pcarlss/Solar-Panel-Cleaning-Drone/Videos and Pictures/image.png

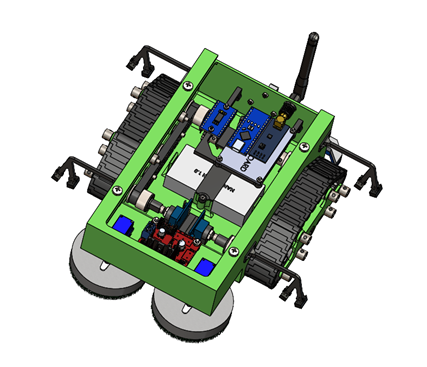
Videos and Pictures/image.png
