pcarlss/Solar-Panel-Cleaning-Drone/Simulations/Rover-Simulation/rover_mission.gif

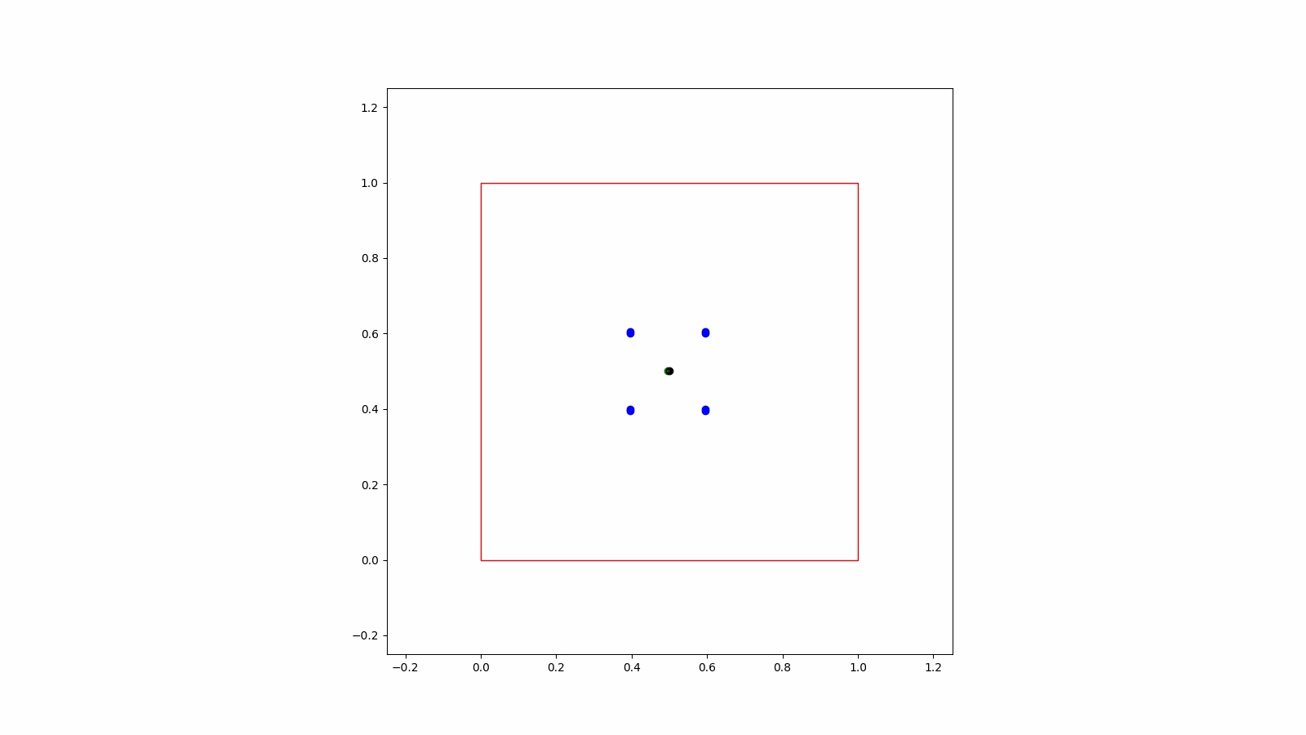
Simulations/Rover-Simulation/rover_mission.gif
