pcarlss/Solar-Panel-Cleaning-Drone/Videos and Pictures/ISO_FINAL.JPG

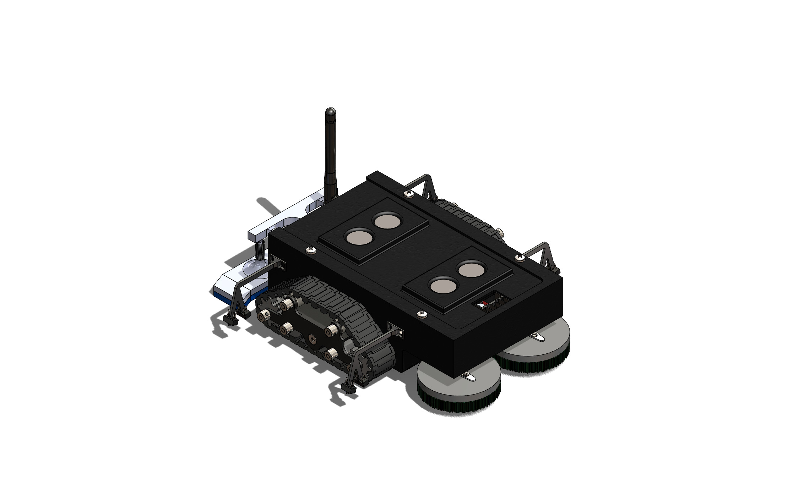
Videos and Pictures/ISO_FINAL.JPG
