pcarlss/Solar-Panel-Cleaning-Drone/KiCad/Complete-Drone-Systems/DronePower.kicad_sch

## KiCad design KiCad/Complete-Drone-Systems/DronePower.kicad_sch (2025-04-15, an earlier design)

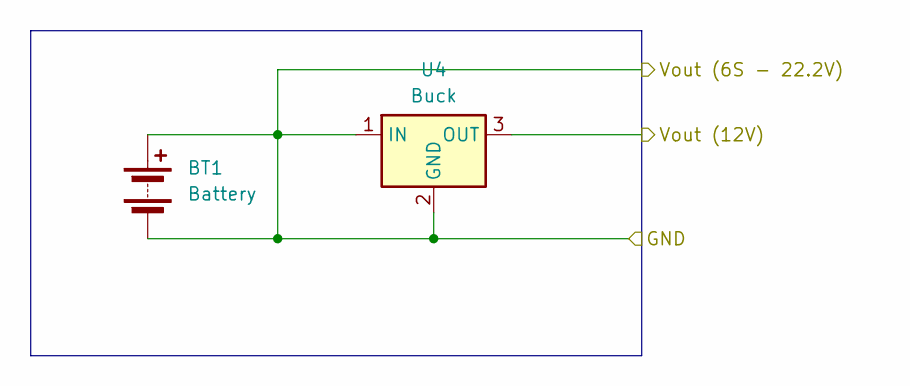
[picture p38: schematic DronePower.kicad_sch]

Parts:
BT1: Battery
U4: Buck; Converter_DCDC_Murata_OKI-78SR_Vertical

Connections:
GND: BT1.1 (+), BT1.2 (-), U4.1 (IN), U4.2 (GND)
Vout (12V): U4.3 (OUT)
