pcarlss/Solar-Panel-Cleaning-Drone/KiCad/Complete-Drone-Systems/Flight.kicad_sch

## KiCad design KiCad/Complete-Drone-Systems/Flight.kicad_sch (2025-01-29)

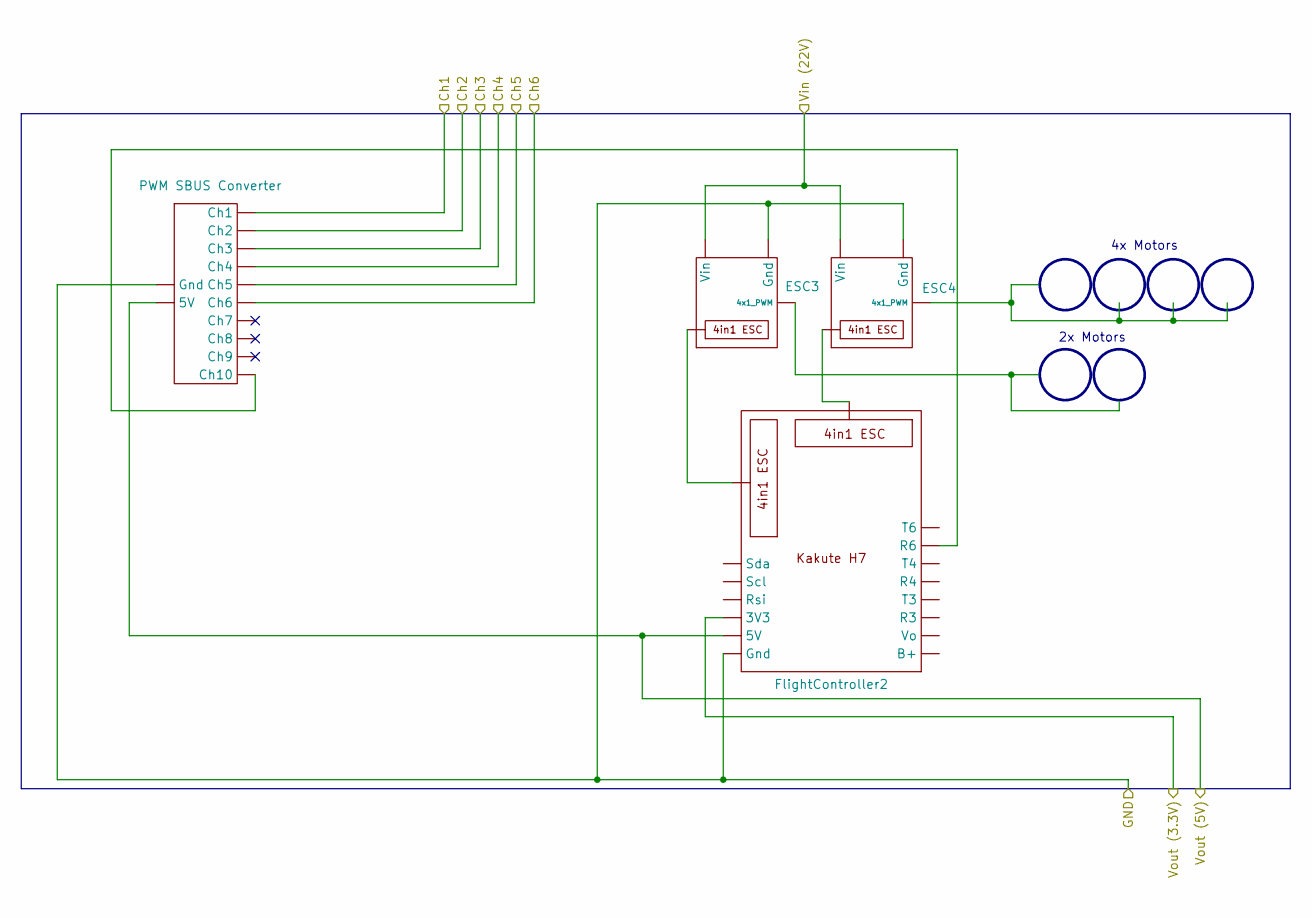
[picture p39: schematic Flight.kicad_sch]

Parts:
ESC3, ESC4: (no value)
FlightController2: (no value)
U6: PWM SBUS Converter

Connections:
Ch1: U6.
Ch2: U6.
Ch3: U6.
Ch4: U6.
Ch5: U6.
Ch6: U6.
GND: ESC3., ESC4., FlightController2., U6.
unnamed: ESC3., FlightController2.
unnamed: ESC4., FlightController2.
unnamed: FlightController2., U6.
Vin (22V): ESC3., ESC4.
Vout (3.3V): FlightController2.
Vout (5V): FlightController2., U6.

Notes on the sheet:
2x Motors
4x Motors
