pcarlss/Solar-Panel-Cleaning-Drone/KiCad/Complete-Drone-Systems/REleaseMechanism.kicad_sch

## KiCad design KiCad/Complete-Drone-Systems/REleaseMechanism.kicad_sch (2025-01-29)

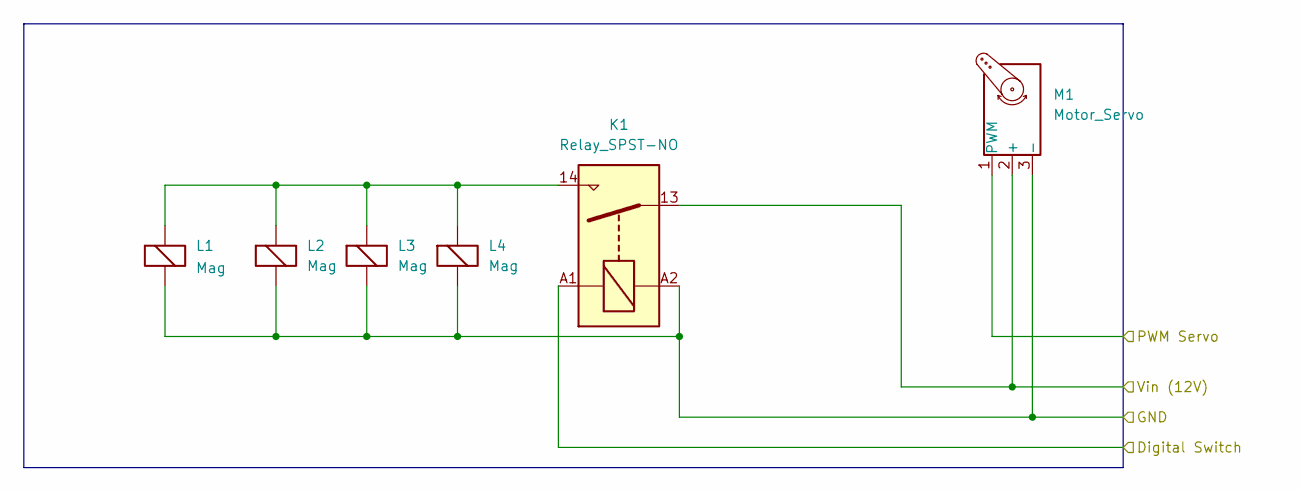
[picture p40: schematic REleaseMechanism.kicad_sch]

Parts:
K1: Relay_SPST-NO
L1, L2, L3, L4: Mag
M1: Motor_Servo

Connections:
Digital Switch: K1.A1
GND: K1.A2, L1.2 (+), L2.2 (+), L3.2 (+), L4.2 (+), M1.3 (-)
unnamed: K1.14, L1.1 (-), L2.1 (-), L3.1 (-), L4.1 (-)
PWM Servo: M1.1 (PWM)
Vin (12V): K1.13, M1.2 (+)
