pcarlss/Solar-Panel-Cleaning-Drone/KiCad/Complete-Drone-Systems/RadioModule.kicad_sch

## KiCad design KiCad/Complete-Drone-Systems/RadioModule.kicad_sch (2025-01-29)

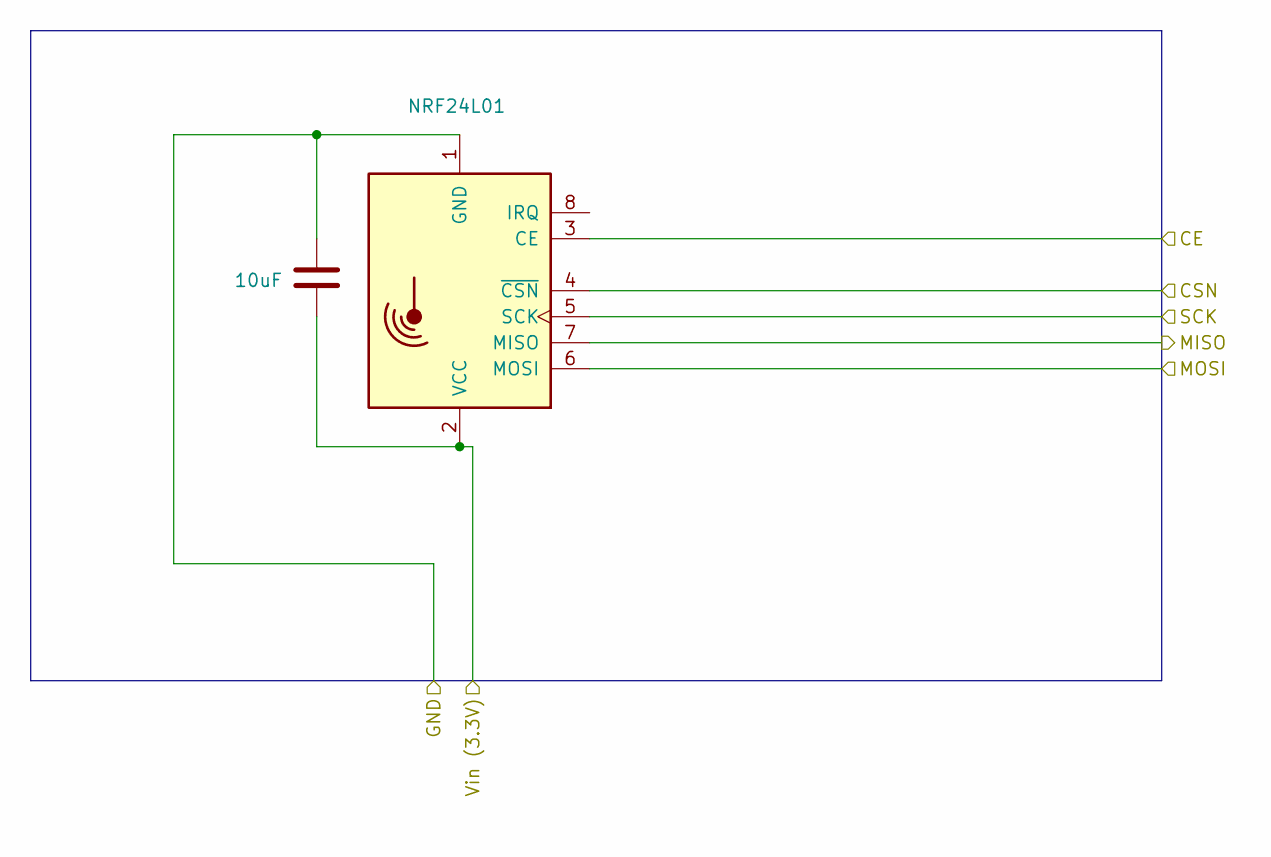
[picture p41: schematic RadioModule.kicad_sch]

Parts:
C2: 10uF
U3: NRF24L01; nRF24L01_Breakout

Connections:
CE: U3.3 (CE)
CSN: U3.4 (~CSN)
GND: C2.2, U3.1 (GND)
MISO: U3.7 (MISO)
MOSI: U3.6 (MOSI)
SCK: U3.5 (SCK)
Vin (3.3V): C2.1, U3.2 (VCC)
