pcarlss/Solar-Panel-Cleaning-Drone/KiCad/Complete-Rover-Systems/CleaningSystem.kicad_sch

## KiCad design KiCad/Complete-Rover-Systems/CleaningSystem.kicad_sch (2025-01-29)

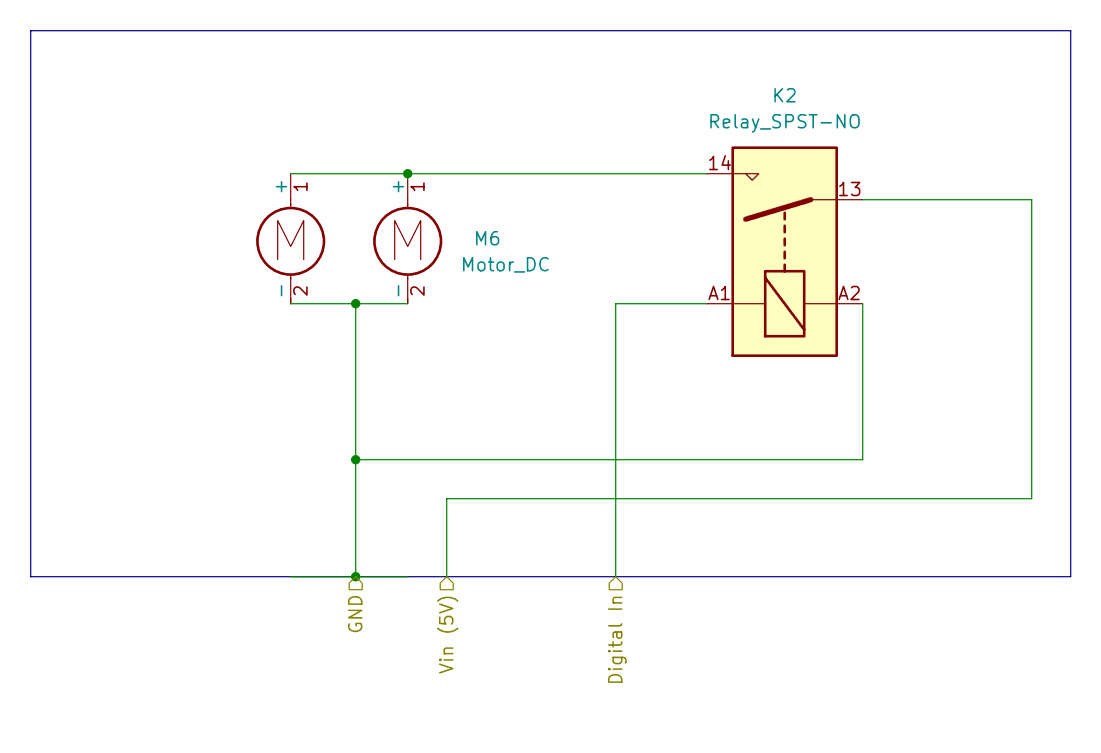
[picture p42: schematic CleaningSystem.kicad_sch]

Parts:
K2: Relay_SPST-NO
M5, M6: Motor_DC

Connections:
Digital In: K2.A1
GND: K2.A2, M5.2 (-), M6.2 (-)
unnamed: K2.14, M5.1 (+), M6.1 (+)
Vin (5V): K2.13
