pcarlss/Solar-Panel-Cleaning-Drone/KiCad/Complete-Rover-Systems/EdgeDetection.kicad_sch

## KiCad design KiCad/Complete-Rover-Systems/EdgeDetection.kicad_sch (2025-04-15, an earlier design)

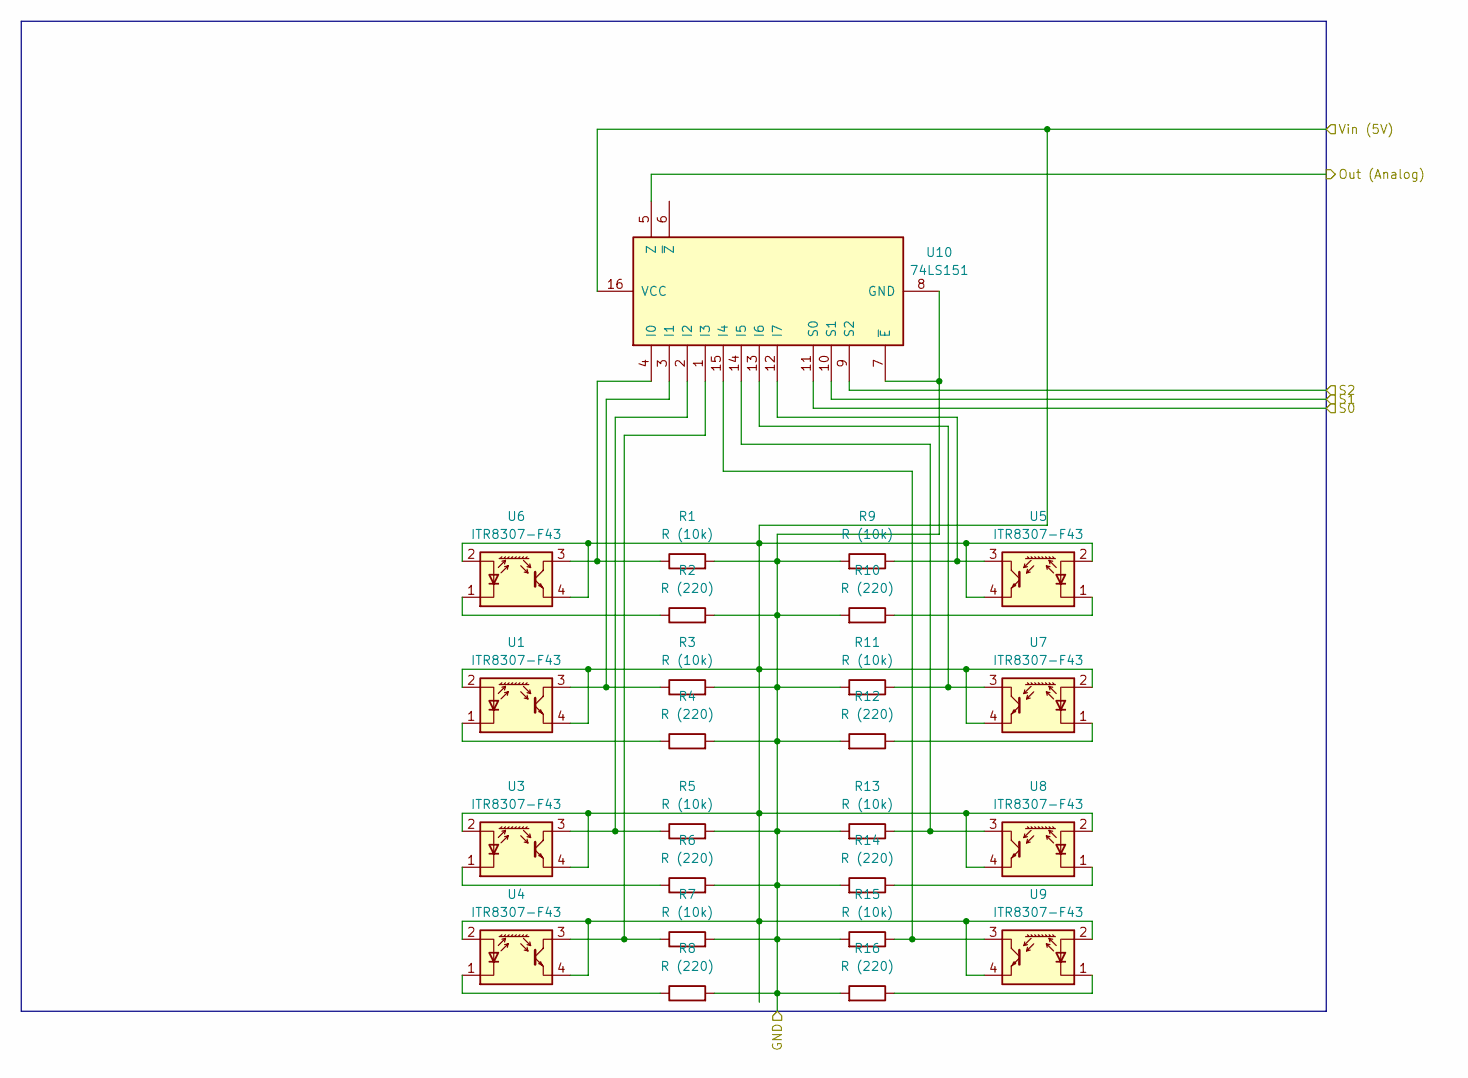
[picture p43: schematic EdgeDetection.kicad_sch]

Parts:
R1, R3, R5, R7, R9, R11, R13, R15: R (10k)
R2, R4, R6, R8, R10, R12, R14, R16: R (220)
U1, U3, U4, U5, U6, U7, U8, U9: ITR8307-F43; Everlight_ITR8307F43
U10: 74LS151

Connections:
GND: R1.2, R2.2, R3.2, R4.2, R5.2, R6.2, R7.2, R8.2, R9.2, R10.2, R11.2, R12.2, R13.2, R14.2, R15.2, R16.2, U10.7 (~E), U10.8 (GND)
unnamed: R1.1, U6.3 (C), U10.4 (I0)
unnamed: R2.1, U6.1 (K)
unnamed: R3.1, U1.3 (C), U10.3 (I1)
unnamed: R4.1, U1.1 (K)
unnamed: R5.1, U3.3 (C), U10.2 (I2)
unnamed: R6.1, U3.1 (K)
unnamed: R7.1, U4.3 (C), U10.1 (I3)
unnamed: R8.1, U4.1 (K)
unnamed: R9.1, U5.3 (C), U10.12 (I7)
unnamed: R10.1, U5.1 (K)
unnamed: R11.1, U7.3 (C), U10.13 (I6)
unnamed: R12.1, U7.1 (K)
unnamed: R13.1, U8.3 (C), U10.14 (I5)
unnamed: R14.1, U8.1 (K)
unnamed: R15.1, U9.3 (C), U10.15 (I4)
unnamed: R16.1, U9.1 (K)
Out (Analog): U10.5 (Z)
S0: U10.11 (S0)
S1: U10.10 (S1)
S2: U10.9 (S2)
Vin (5V): U1.2 (A), U1.4 (E), U3.2 (A), U3.4 (E), U4.2 (A), U4.4 (E), U5.2 (A), U5.4 (E), U6.2 (A), U6.4 (E), U7.2 (A), U7.4 (E), U8.2 (A), U8.4 (E), U9.2 (A), U9.4 (E), U10.16 (VCC)
