pcarlss/Solar-Panel-Cleaning-Drone/KiCad/Complete-Rover-Systems/RadioModule.kicad_sch

## KiCad design KiCad/Complete-Rover-Systems/RadioModule.kicad_sch (2025-01-29)


Parts:
C1: 10uF
U11: NRF24L01; nRF24L01_Breakout

Connections:
CE: U11.3 (CE)
CSN: U11.4 (~CSN)
GND: C1.2, U11.1 (GND)
MISO: U11.7 (MISO)
MOSI: U11.6 (MOSI)
SCK: U11.5 (SCK)
Vin (3.3V): C1.1, U11.2 (VCC)
