pcarlss/Solar-Panel-Cleaning-Drone/KiCad/Complete-Rover-Systems/TrackSystem.kicad_sch

## KiCad design KiCad/Complete-Rover-Systems/TrackSystem.kicad_sch (2025-01-29)

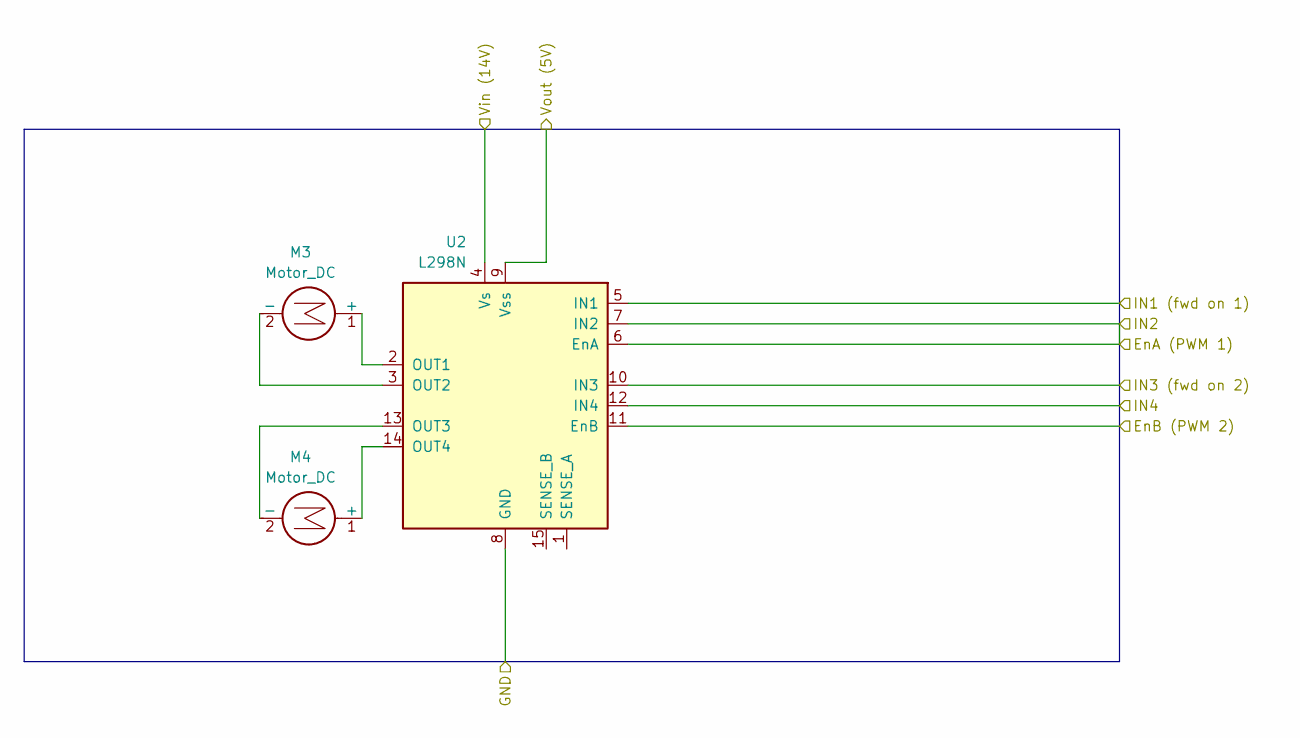
[picture p44: schematic TrackSystem.kicad_sch]

Parts:
M3, M4: Motor_DC
U2: L298N; TO-220-15_P2.54x2.54mm_StaggerOdd_Lead4.58mm_Vertical

Connections:
EnA (PWM 1): U2.6 (EnA), U2.7 (IN2)
EnB (PWM 2): U2.11 (EnB)
GND: U2.8 (GND)
IN1 (fwd on 1): U2.5 (IN1)
IN3 (fwd on 2): U2.10 (IN3)
IN4: U2.12 (IN4)
unnamed: M3.1 (+), U2.2 (OUT1)
unnamed: M3.2 (-), U2.3 (OUT2)
unnamed: M4.1 (+), U2.14 (OUT4)
unnamed: M4.2 (-), U2.13 (OUT3)
Vin (14V): U2.4 (Vs)
Vout (5V): U2.9 (Vss)
