pcarlss/Solar-Panel-Cleaning-Drone/Arduino/[1] In-Use/Control_V5/Control_V5.ino

#include "SPI.h"
#include "RF24.h"
#include "nRF24L01.h"
#include <XBOXONE.h>
#include <usbhub.h>
#include <Wire.h>
#include <LiquidCrystal_I2C.h>

/////////////////////////////////////////////////////////////////////////////
/////////////////// DEFINITIONS AND VARIABLES ///////////////////////////////

#define INTERVAL_MS_TRANSMISSION 1
#define LCD_UPDATE_INTERVAL 100
#define CE_PIN 6   // CE pin for RF24
#define CSN_PIN 7  // CSN pin for RF24
#define RAMP_UP_SPEED 10
#define RAMP_DOWN_THROTTLE 30
#define RAMP_DOWN_SPEED 10

unsigned long lastRadioSuccess = 0;
unsigned long lastUsbSuccess = 0;
const unsigned long RADIO_TIMEOUT = 500;  // 0.5 seconds
const unsigned long USB_TIMEOUT = 500;    // 0.5 seconds
unsigned long timeLCD = 0;
unsigned long lastLCD = 0;

RF24 radio(CE_PIN, CSN_PIN);
const byte address[6] = "00001";

USB Usb;
XBOXONE Xbox(&Usb);
LiquidCrystal_I2C lcd(0x27, 16, 2);

uint8_t usbstate;
uint8_t laststate = 0;
USB_DEVICE_DESCRIPTOR buf;

bool radioInitialized = false;
unsigned long lastLcdUpdate = 0;
bool freezeDisplay = false;
int scrollPosition = 0;

float servoAngle = 90;

bool toggleSafety = 1;
String safety = " Unarmed";

bool startButtonPrevState = 0;
int RBPrevState = 0;
int LBPrevState = 0;
int display = 5;

bool toggleHover = 1;
String hover = "Free";
float hoverThrottleValue = 0;

int missionPercentage = 0;

int Dbat = 50;
int Rbat = 100;

bool droneAdminStatus = false;

struct ControllerData {
  int roll;
  int pitch;
  int throttle;
  int yaw;
  int angle;
  int safety;
  bool AUX;
} ControllerData;

/////////////////////////////////////////////////////////////////////////////
/////////////////// VOID SETUP //////////////////////////////////////////////

void setup() {
  Serial.begin(115200);
#if !defined(__MIPSEL__)
  while (!Serial)
    ;
#endif
  if (Usb.Init() == -1) {
    Serial.println("USB Host initialization failed");
    while (1)
      ;
  } else Serial.println("USB Host initialization success");

  initializeRadio();

  lcd.init();
  lcd.backlight();
  lcd.setCursor(2, 0);
  lcd.print("[SPCD Start]");
  lcd.setCursor(1, 1);
  lcd.print("Capstone  2025");
  delay(1500);
}

void initializeRadio() {
  radio.begin();
  if (!radio.isChipConnected()) {
    Serial.println("Radio not connected. Please check your wiring.");
    lcd.clear();
    lcd.print("Radio Error");
    delay(1000);
    while (1)
      ;  // Stop the program if the radio is not connected
  } else if (radio.isChipConnected()) {
    lcd.clear();
    lcd.setCursor(1, 0);
    lcd.print("Radio Success");
    delay(1000);
  }

  radio.setAutoAck(false);        // (true|false)
  radio.setDataRate(RF24_1MBPS);  // (RF24_250KBPS|RF24_1MBPS|RF24_2MBPS)
  radio.setPALevel(RF24_PA_MIN);  // (RF24_PA_MIN|RF24_PA_LOW|RF24_PA_HIGH|RF24_PA_MAX)
  radio.setPayloadSize(sizeof(ControllerData));
  radio.openWritingPipe(address);
  radio.setChannel(100);
  radio.stopListening();

  Serial.println("Radio initialized");
  radioInitialized = true;  // Mark radio as initialized
}

/////////////////////////////////////////////////////////////////////////////
/////////////////// SCROLL LCD FUNCTION /////////////////////////////////////

// void scrollString(String message) {
//   // Clear the display and print the message at the start
//   lcd.clear();
//   lcd.print(message);

//   // Calculate the length of the message
//   int messageLength = message.length();

//   // Scroll the message if it's longer than 16 characters
//   if (messageLength > 16) {
//     // Loop through the message to create a scrolling effect
//     for (int position = 0; position <= messageLength - 16; position++) {
//       lcd.setCursor(0, 0);                                    // Move cursor to the beginning
//       lcd.print(message.substring(position, position + 16));  // Print the substring
//       delay(150);                                             // Introduce a small delay to control the scrolling speed
//     }

//     // Wait until the message is completely off the screen
//     for (int position = messageLength - 16; position < messageLength; position++) {
//       lcd.setCursor(0, 0);                                    // Move cursor to the beginning
//       lcd.print("                ");                          // Clear the line for scrolling effect
//       lcd.setCursor(0, 0);                                    // Move cursor to the beginning
//       lcd.print(message.substring(position, position + 16));  // Print the substring
//       delay(150);                                             // Introduce a small delay to control the scrolling speed
//     }

//     // Clear the display to remove any remaining characters
//     lcd.clear();
//   } else {
//     // If the message fits, print it without scrolling
//     lcd.clear();
//     lcd.print(message);
//   }
// }

int rampToTarget(int currentValue, int targetValue, int rampUpSpeed, int rampDownSpeed) {
  if (currentValue < targetValue) {
    return min(currentValue + rampUpSpeed, targetValue);  // Ramp up
  } else if (currentValue > targetValue) {
    return max(currentValue - rampDownSpeed, targetValue);  // Ramp down
  }
  return currentValue;  // No change needed
}

/////////////////////////////////////////////////////////////////////////////
/////////////////// VOID LOOP MAIN //////////////////////////////////////////

void loop() {
  Usb.Task();
  usbstate = Usb.getUsbTaskState();

  if (usbstate != laststate) {
    laststate = usbstate;
    switch (usbstate) {
      case USB_DETACHED_SUBSTATE_WAIT_FOR_DEVICE:
        Serial.println("Waiting for device...");
        // scrollString("        Awaiting RC signal");
        lcd.clear();
        lcd.setCursor(3, 0);
        lcd.print("Insert USB");
        break;
      case USB_ATTACHED_SUBSTATE_RESET_DEVICE:
        Serial.println("Device connected. Resetting...");
        // scrollString("Device connected.");
        break;
      case USB_ATTACHED_SUBSTATE_WAIT_SOF:
        Serial.println("Reset complete. Waiting for the first SOF...");
        // scrollString("Reset complete. Waiting for SOF...");
        lcd.clear();
        lcd.setCursor(3, 0);
        lcd.print("USB Active");
        delay(1000);
        lcd.clear();
        break;
      case USB_ATTACHED_SUBSTATE_GET_DEVICE_DESCRIPTOR_SIZE:
        Serial.println("SOF generation started. Enumerating device...");
        // scrollString("SOF generation started...");
        break;
      case USB_STATE_ADDRESSING:
        Serial.println("Setting device address...");
        // scrollString("Setting device address...");
        break;
      case USB_STATE_RUNNING:
        Serial.println("Getting device descriptor...");
        // scrollString("Getting device descriptor...");
        uint8_t rcode = Usb.getDevDescr(1, 0, sizeof(USB_DEVICE_DESCRIPTOR), (uint8_t*)&buf);
        if (rcode) {
          Serial.print("Error reading device descriptor. Error code: ");
          Serial.println(rcode, HEX);
        } else {
          Serial.print("Vendor ID: ");
          Serial.println(buf.idVendor, HEX);
          Serial.print("Product ID: ");
          Serial.println(buf.idProduct, HEX);
        }
        break;
      case USB_STATE_ERROR:
        Serial.println("USB state machine reached error state");
        break;
      default:
        break;
    }
  }

  if (Xbox.XboxOneConnected) {
    const int DEAD_ZONE = 7500;

    int throttleInput = Xbox.getAnalogHat(LeftHatY);
    int yawInput = Xbox.getAnalogHat(LeftHatX);
    int pitchInput = Xbox.getAnalogHat(RightHatY);
    int rollInput = Xbox.getAnalogHat(RightHatX);
    int leftTrigger = Xbox.getButtonPress(LT);
    int rightTrigger = Xbox.getButtonPress(RT);
    int start = Xbox.getButtonPress(START);
    int RB = Xbox.getButtonPress(R1);
    int LB = Xbox.getButtonPress(L1);

    if (start && !startButtonPrevState && display == 0) {
      toggleSafety = !toggleSafety;
      switch (toggleSafety) {
        case 0:
          lcd.clear();
          safety = " Armed";
          break;
        default:
          lcd.clear();
          safety = "Disarmed";
          break;
      }
    } else if (start && !startButtonPrevState && display == 1) {
      toggleHover = !toggleHover;
      switch (toggleHover) {
        case 0:
          lcd.clear();
          hover = "Hold";
          hoverThrottleValue = ControllerData.throttle = (abs(throttleInput) < DEAD_ZONE) ? 1000 : rampToTarget(ControllerData.throttle, map(throttleInput, -32767, 32767, 1000, 2000), RAMP_UP_SPEED, RAMP_DOWN_SPEED);
          break;
        default:
          lcd.clear();
          hover = "Free";
          break;
      }
    }
    else if (start && !startButtonPrevState && display == 5) {
      droneAdminStatus = !droneAdminStatus;
    }
    startButtonPrevState = start;

    if (RB && !RBPrevState) {
      if (display == 5) display = 0;
      else display++;
      lcd.clear();
    }
    RBPrevState = RB;

    if (LB && !LBPrevState) {
      if (display == 0) display = 5;
      else display--;
      lcd.clear();
    }
    LBPrevState = LB;

    bool leftTriggerActive = false;
    bool rightTriggerActive = false;

    if (display == 0) {
      if (leftTrigger > 800) {
        if (!leftTriggerActive && servoAngle > 0) {
          servoAngle -= 0.25;
          leftTriggerActive = true;
        }
      } else {
        leftTriggerActive = false;
      }

      if (rightTrigger > 800) {
        if (!rightTriggerActive && servoAngle < 180) {
          servoAngle += 0.25;
          rightTriggerActive = true;
        }
      } else {
        rightTriggerActive = false;
      }
    } else if (display == 1) {
      if (leftTrigger > 800) {
        if (!leftTriggerActive && hoverThrottleValue > 1000) {
          hoverThrottleValue -= 0.25;
          leftTriggerActive = true;
        }
      } else {
        leftTriggerActive = false;
      }

      if (rightTrigger > 800) {
        if (!rightTriggerActive && hoverThrottleValue < 2000) {
          hoverThrottleValue += 0.25;
          rightTriggerActive = true;
        }
      } else {
        rightTriggerActive = false;
      }
    }



    if (hover == "Free") {
      ControllerData.throttle = (abs(throttleInput) < DEAD_ZONE)
                                  ? rampToTarget(ControllerData.throttle, 1000, RAMP_UP_SPEED, RAMP_DOWN_THROTTLE)
                                  : rampToTarget(ControllerData.throttle, map(throttleInput, -32767, 32767, 1000, 2000), RAMP_UP_SPEED, RAMP_DOWN_SPEED);
    } else ControllerData.throttle = int(hoverThrottleValue);
    ControllerData.yaw = (abs(yawInput) < DEAD_ZONE)
                           ? rampToTarget(ControllerData.yaw, 1500, RAMP_UP_SPEED, RAMP_DOWN_SPEED)
                           : rampToTarget(ControllerData.yaw, map(yawInput, -32767, 32767, 1425, 1575), RAMP_UP_SPEED, RAMP_DOWN_SPEED);

    ControllerData.pitch = (abs(pitchInput) < DEAD_ZONE)
                             ? rampToTarget(ControllerData.pitch, 1500, RAMP_UP_SPEED, RAMP_DOWN_SPEED)
                             : rampToTarget(ControllerData.pitch, map(pitchInput, -32767, 32767, 1425, 1575), RAMP_UP_SPEED, RAMP_DOWN_SPEED);

    ControllerData.roll = (abs(rollInput) < DEAD_ZONE)
                            ? rampToTarget(ControllerData.roll, 1500, RAMP_UP_SPEED, RAMP_DOWN_SPEED)
                            : rampToTarget(ControllerData.roll, map(rollInput, -32767, 32767, 1425, 1575), RAMP_UP_SPEED, RAMP_DOWN_SPEED);

    ControllerData.safety = toggleSafety;
    ControllerData.angle = int(servoAngle);
    ControllerData.AUX = droneAdminStatus;

    // Serial.print("Throttle: ");
    // Serial.print(ControllerData.throttle);
    // Serial.print(", Yaw: ");
    // Serial.print(ControllerData.yaw);
    // Serial.print(", Pitch: ");
    // Serial.print(ControllerData.pitch);
    // Serial.print(", Roll: ");
    // Serial.println(ControllerData.roll);
    Serial.println(ControllerData.AUX);

    timeLCD = millis();
    switch (display) {
      case 0:
        if ((timeLCD - lastLCD) >= LCD_UPDATE_INTERVAL) {
          lastLCD = timeLCD;
          lcd.setCursor(1, 0);
          lcd.print("[RELEASE TAB ]");
          lcd.setCursor(1, 1);
          lcd.print(safety);

          if (safety == " Armed") {
            if (servoAngle >= 100) lcd.setCursor(9, 1);
            else if (servoAngle >= 10) {
              lcd.setCursor(9, 1);
              lcd.print(" ");
            } else {
              lcd.setCursor(9, 1);
              lcd.print("  ");
            }
            lcd.print(int(servoAngle));
            lcd.setCursor(12, 1);
            lcd.print(char(223));
          } else {
            if (servoAngle >= 100) lcd.setCursor(10, 1);
            else if (servoAngle >= 10) {
              lcd.setCursor(10, 1);
              lcd.print(" ");
            } else {
              lcd.setCursor(10, 1);
              lcd.print("  ");
            }
            lcd.print(int(servoAngle));
            lcd.setCursor(13, 1);
            lcd.print(char(223));
          }
        }
        break;
      case 1:
        if ((timeLCD - lastLCD) >= LCD_UPDATE_INTERVAL) {
          lastLCD = timeLCD;
          lcd.setCursor(1, 0);
          lcd.print("[AUTO HOV TAB]");

          lcd.setCursor(2, 1);
          lcd.print(hover);

          lcd.setCursor(8, 1);
          lcd.print("T:");

          if (hover == "Hold") {
            if (hoverThrottleValue >= 1000) lcd.setCursor(10, 1);
            else if (hoverThrottleValue >= 100) {
              lcd.setCursor(10, 1);
              lcd.print(" ");
            } else if (hoverThrottleValue >= 10) {
              lcd.setCursor(10, 1);
              lcd.print("  ");
            } else {
              lcd.setCursor(10, 1);
              lcd.print("   ");
            }
            lcd.print((int)hoverThrottleValue);
          } else {
            lcd.print(ControllerData.throttle);
          }
          break;
        }
      case 2:
        if ((timeLCD - lastLCD) >= LCD_UPDATE_INTERVAL) {
          lastLCD = timeLCD;
          lcd.setCursor(1, 0);
          lcd.print("[ ROVER TAB  ]");

          lcd.setCursor(3, 1);
          lcd.print("Path: ");
          lcd.print(missionPercentage);
          lcd.print("%");
        }
        break;
      case 3:
        if ((timeLCD - lastLCD) >= LCD_UPDATE_INTERVAL) {
          lastLCD = timeLCD;
          lcd.setCursor(1, 0);
          lcd.print("[BATTERY TAB ]");
          lcd.setCursor(1, 1);
          lcd.print("D: ");
          lcd.print(Dbat);
          lcd.print("%");
          lcd.setCursor(9, 1);
          lcd.print("R: ");
          lcd.print(Rbat);
          lcd.print("%");
        }
        break;
      case 4:
        if ((timeLCD - lastLCD) >= LCD_UPDATE_INTERVAL) {
          lastLCD = timeLCD;

          // Calculate uptime in seconds
          unsigned long uptime = timeLCD / 1000;  // Convert milliseconds to seconds

          // Calculate hours, minutes, and seconds
          unsigned long hours = uptime / 3600;
          unsigned long minutes = (uptime % 3600) / 60;
          unsigned long seconds = uptime % 60;

          lcd.setCursor(1, 0);
          lcd.print("[SERVICE TIME]");
          lcd.setCursor(4, 1);
          if (hours < 10) lcd.print("0");
          lcd.print(hours);
          lcd.print(":");
          if (minutes < 10) lcd.print("0");
          lcd.print(minutes);
          lcd.print(":");
          if (seconds < 10) lcd.print("0");
          lcd.print(seconds);
        }
        break;
      case 5:
        if ((timeLCD - lastLCD) >= LCD_UPDATE_INTERVAL) {
          lastLCD = timeLCD;
          lcd.setCursor(1, 0);
          lcd.print("[ STATUS TAB ]");
          lcd.setCursor(1, 1);
          if (droneAdminStatus) lcd.print(" Drone Armed    ");
          else lcd.print("Drone Disarmed");
        }
        break;
    }
  }

  radio.write(&ControllerData, sizeof(ControllerData));
  delay(INTERVAL_MS_TRANSMISSION);
}
