pcarlss/Solar-Panel-Cleaning-Drone/Simulations/Rover-Simulation/testing.py

import random
import matplotlib.pyplot as plt
import matplotlib.patches as patches
import numpy as np
from scipy import signal
from matplotlib.animation import FuncAnimation
import matplotlib.animation as animation
from components import DCMotorDiscrete, SimpleMotor, PIDController, RotaryEncoder, IMU
from area import SolarPanelArea
from rover import Rover
from scipy.interpolate import UnivariateSpline
from common import RadioMessage, SearchForCornerStates, OuterLoopStates, InnerLoopStates

from error import GaussianProportionalError, GaussianDerivativeError, GaussianNoise, GaussMarkovBias


def imu_test():
    dt=0.1

    accel_func_list = [
        lambda x: 0,
        lambda x: -1,
        lambda x: 0,
        lambda x: 1,
        lambda x: 0, 
        lambda x: 1,
        lambda x: 0,
        lambda x: -1,
        lambda x: 0
    ]
    condition_list = lambda x: [
        x >= 0,
        x >= 10,
        x >= 15,
        x >= 30,
        x >= 35,
        x >= 50,        
        x >= 55,
        x >= 70,
        x >= 75,

    ]
    xs = np.arange(0,200,dt)
    piecewise_accels = np.piecewise(xs, condlist=condition_list(xs), funclist=accel_func_list)
    piecewise_velocities = np.cumsum(piecewise_accels*dt)
    piecewise_positions = np.cumsum(piecewise_velocities*dt)

    # error_model = GaussianProportionalError(k=0.5,s0=0.001,dt=dt)
    error_model = GaussianNoise(20, 0.1)

    measured_accels = error_model.apply(piecewise_accels)
    measured_velocities = np.cumsum(measured_accels*dt)
    measured_positions = np.cumsum(measured_velocities*dt)

    fig, axs = plt.subplots(2,3)
    
    fig.set_size_inches(9, 9)
    
    plt.setp(axs, xlim=(0,200))
                

    m_a, = axs[0,0].plot(xs, measured_accels, 'r-')
    p_a, = axs[0,0].plot(xs, piecewise_accels, 'k--')
    axs[0,0].set_title("Acceleration")

    m_v, = axs[0,1].plot(xs, measured_velocities, 'r-')
    p_v, = axs[0,1].plot(xs, piecewise_velocities, 'k--')
    axs[0,1].set_title("Velocity")

    m_p, = axs[0,2].plot(xs, measured_positions, 'r-')
    p_p, = axs[0,2].plot(xs, piecewise_positions, 'k--')
    axs[0,2].set_title("Position")

    a_e, = axs[1,0].plot(xs, piecewise_accels-measured_accels)
    axs[1,0].set_title("Acceleration Error")

    v_e, = axs[1,1].plot(xs, piecewise_velocities-measured_velocities)
    axs[1,1].set_title("Velocity Error")

    p_e, = axs[1,2].plot(xs, piecewise_positions-measured_positions)
    axs[1,2].set_title("Position Error")
    
    # def animate(i):
    #     x = xs[:i]
    #     m_a.set_data(x, measured_accels[:i])
    #     p_a.set_data(x, piecewise_accels[:i])
    #     m_v.set_data(x, measured_velocities[:i])
    #     p_v.set_data(x, piecewise_velocities[:i])
    #     m_p.set_data(x, measured_positions[:i])
    #     p_p.set_data(x, piecewise_positions[:i])
    #     a_e.set_data(x, (piecewise_accels-measured_accels)[:i])
    #     v_e.set_data(x, (piecewise_velocities-measured_velocities)[:i])
    #     p_e.set_data(x, (piecewise_positions-measured_positions)[:i])
    #     return m_a, p_a, m_v, p_v, m_p, p_p, a_e, v_e, p_e
    
    # ani = FuncAnimation(
    #     fig,
    #     animate,
    #     interval=1,
    #     blit=False,
    #     frames=range(len(xs)),
    #     repeat_delay=100
    # )
    
    # writer = animation.PillowWriter(fps=15,
    #                                 bitrate=1800)
    # ani.save('imu.gif', writer=writer)


    plt.tight_layout()
    plt.show()


    pass

def gauss_error_test():
    x = np.linspace(0, 10, 100)
    real_y = np.sin(x)

    errormodel = GaussianProportionalError(0.1, 0.005, q=0.1, minval=-1, maxval=1)
    measure_y = np.array(list(map(lambda x: errormodel.apply(x, discretize=True), real_y,)))

    plt.plot(x, real_y, 'k--')
    plt.step(x, measure_y, 'r-')
    plt.xlim(np.min(x), np.max(x))
    plt.ylim(np.min(np.append(real_y, measure_y)),np.max(np.append(real_y, measure_y)))
    plt.show()
    pass

def derivative_error_test():
    q = 0.01
    x = np.arange(-2, 2, q)
    real_y = np.sin(x**2)
    real_y_prev = np.insert(real_y, 0, values=0)

    errormodel = GaussianDerivativeError(0.05, s0=0.005, q=q)
    measure_y = np.array(list(map(lambda x, x_prev: errormodel.apply(x, x_prev, discretize=True), real_y, real_y_prev)))

    plt.step(x, measure_y, 'r-')
    plt.plot(x, real_y, 'k--')

    plt.xlim(np.min(x), np.max(x))
    plt.ylim(np.min(np.append(real_y, measure_y)),np.max(np.append(real_y, measure_y)))
    plt.show()
    pass

def visualization_test():
    # Working test code for scrolling visualization window -- not hooked up to any sim elements yet
    x = [1]
    y = [random.randint(1,10)]

    xbuf = 100

    # creating the first plot and frame
    fig, ax = plt.subplots()
    graph = ax.plot(x,y,color = 'g')[0]
    
    plt.ylim(0,10)
    # updates the data and graph
    def update(frame):
        
        # updating the data
        x.append(x[-1] + 1)
        y.append(random.randint(1,10))

        # creating a new graph or updating the graph
        graph.set_xdata(x)
        graph.set_ydata(y)
        if len(x) >= xbuf:
            plt.xlim(x[-1*xbuf], x[-1])
        else: 
            plt.xlim(x[0], x[-1])
            
    
    
    anim = FuncAnimation(fig, update, frames = len(x), interval = 10, cache_frame_data=False)
    
    plt.show()    

def motor_test():
    dt = 0.01  # Time step [s]
    sim_time = 5.0  # Total simulation time [s]
    steps = int(sim_time/dt)

    motor = DCMotorDiscrete(K=1.14, J=4.785E-4, L=10e-3, R=30, dt=dt)
    pid = PIDController(Kp=0.15, Ki=3, Kd=0, Kff=3.779, dt=dt)
    
    # motor = SimpleMotor()
    # pid = PIDController(Kp=0, Ki=5, Kd=0, dt=dt)

    time = np.zeros(steps)
    speed = np.zeros(steps)
    target = np.zeros(steps)
    voltage_input = np.zeros(steps)
    
    # Simulation loop
    for i in range(steps):
        # Update target speed at specific times
        control_voltage=12*(i/steps)
        if i < 100:
            new_target = 0
            # control_voltage=0
        elif i < 300:
            new_target = 3
            # control_voltage=12            
        else:
            new_target = -3
            # control_voltage=-12
        
        # Get current speed
        
        current_speed = motor.get_speed()
        
        # Calculate control voltage using PID controller
        control_voltage = pid.calculate(new_target, current_speed)
        
        # Update motor state with the control voltage
        motor.update(control_voltage)
        
        # Record values
        time[i] = i * dt
        speed[i] = current_speed
        target[i] = new_target
        voltage_input[i] = max(min(control_voltage,12),-12)
    
    # Plot results
    plt.figure(figsize=(9, 9))
    
    plt.plot(time, target, 'r--', label='Target Speed')
    plt.plot(time, speed, 'b-', label='Actual Speed')
    plt.plot(time, voltage_input, 'g--', label='Control Voltage')
    plt.xlim(0,5)
    # plt.ylim(-12.5,12.5)
    
    plt.xlabel('Time [s]')
    plt.ylabel('Angular Velocity [rad/s] / Voltage [V]')
    plt.title('Motor Speed Tracking with PID Control')
    plt.grid(True)
    plt.legend()
    plt.tight_layout()
    plt.show()   
    print(target)

def panel_test():
    a = SolarPanelArea(1, 1, 10)
    print(a.locate_round(0.74, 0.76)) 

def rover_movement_test():
    panel = SolarPanelArea(10,10,1000)
    plot_xs = []
    plot_ys = []
    or_xs, or_ys = [], []
    time_step = 0.01
    time_stop = 5
    time_arange = np.arange(0, time_stop, time_step)

    rover = Rover(panel, time_step)
    rover.set_trajectory(0.1,0)

    print(f"Desired speeds: {rover.l_desired_speed, rover.r_desired_speed}")

    for t in range(100):
        rover.update_sensors()
        
    for t in time_arange:
        rover.update_sensors()
        rover.update_motors(use_sensors=True)
        rover.update_position()
        # print(f"Motor State: {rover.update_motors()}")
        # print(f"Motor: {rover.update_position()}")

        plot_xs.append(rover.positional_information.position[0])
        plot_ys.append(rover.positional_information.position[1])
        or_xs.append(rover.positional_information.orientation[0])
        or_ys.append(rover.positional_information.orientation[1])
        
        

    
    fig, ax = plt.subplots(1,1)
    path, = ax.plot(plot_xs, plot_ys, 'k--', label='Rover path')
    r_point, = ax.plot(0,0,"ro", label='Rover CG')
    
    ax.set_xlim(-0.05,0.5)
    ax.set_ylim(-0.05,0.15)
    
    arr_scale = 0.0075
    or_arrow = ax.arrow(0,0,0,0 , head_width=0.0025, head_length=0.001, color='r', ec=None, label='Rover orientation')
    ax.set_aspect('equal')
    ax.set_title("Rover circular path demonstration")
    ax.legend(loc='center', ncol=1, fancybox=True, shadow=True)

    def animate(i):
        x, y = plot_xs[:i], plot_ys[:i]
        or_x, or_y = or_xs[i], or_ys[i]
        path.set_data(x, y)
        r_point.set_data([x[-1]],[y[-1]])
        or_arrow.set_data(x=x[-1],y=y[-1], dx=arr_scale*or_x, dy=arr_scale*or_y)
        return path, r_point
    
    ani = FuncAnimation(
        fig,
        animate,
        interval=10,
        blit=False,
        frames=range(1,len(plot_xs)),
        repeat_delay=100
    )
    
    writer = animation.PillowWriter(fps=60,
                                    bitrate=1800)
    ani.save('movement.gif', writer=writer)
        
    plt.show()

def rotary_encoder_test():
    time_step = 0.01
    time_stop = 5
    time_arr = np.arange(0,time_stop,time_step)

    encoder = RotaryEncoder(time_step=time_step, zero_time=1)
    encoder_v = []
    encoder_vavg = []
    encoder_p = []
    real_velocity = 1*signal.square(2 * np.pi * time_arr * 1/4)
    
    averaging_period = 3
    
    for v in real_velocity:
        enc_v, enc_p = encoder.get_track_velocity(v)
        encoder_v.append(enc_v)
        encoder_p.append(enc_p)
        if len(encoder_vavg) < averaging_period:
            encoder_vavg.append(enc_v)
        else:
            encoder_vavg.append(np.average(encoder_v[-1*averaging_period:-1]))

    
    plt.plot(time_arr, real_velocity, 'k--')
    plt.plot(time_arr, encoder_v)
    plt.plot(time_arr, encoder_vavg, 'r')
    
    plt.show()

def rover_sensor_movement_test():
    panel = SolarPanelArea(10,10,1000)
    
    time_step = 0.01
    time_stop = 5
    time_arange = np.arange(0, time_stop, time_step)

    rover = Rover(panel, time_step)
    speed_max = 0.02
    rover.set_trajectory(speed_max, 0)

    l_speed_actual = []
    l_speed_enc = []
    r_speed_actual = []
    r_speed_enc = []
    
    l_desired = []
    r_desired = []
    
    x_position = []
    y_position = []
    
    # This initial buffer is NECESSARY to prevent immediate-reversal issues. Also better represents real world situation
    for t in range(100):
        rover.update_sensors()
    
    for t in time_arange:
        # if t == int(t):
        #     speed_max = -1*speed_max
        #     rover.set_trajectory(speed_max, 0)
        x_position.append(rover.positional_information.position[0])
        y_position.append(rover.positional_information.position[1])
        
        l_speed_actual.append(rover.positional_information.l_speed)
        r_speed_actual.append(rover.positional_information.r_speed)
        
        l_desired.append(rover.l_desired_speed)
        r_desired.append(rover.r_desired_speed)
        l_speed_enc.append(rover.estimated_pos.l_speed)
        r_speed_enc.append(rover.estimated_pos.r_speed)
        rover.update_sensors()

        rover.update_motors(use_sensors=True)
        rover.update_position()
        

        
    

    
    fig, (l_plot, r_plot) = plt.subplots(2,1)  
    plt.setp((l_plot, r_plot), xlim=(0,time_stop), xlabel='time [s]', ylabel='Angular velocity [rad/s]')
    
    fig.set_size_inches(9,9)
    l_plot.set_title("Left track velocity")
    r_plot.set_title("Right track velocity")
    
    l_plot.plot(time_arange, l_desired, 'r--', label='Desired Velocity')
    r_plot.plot(time_arange, r_desired, 'r--', label='Desired Velocity')
        
    l_plot.plot(time_arange, l_speed_enc, 'b', lw=0.5, label='Measured Velocity')
    r_plot.plot(time_arange, r_speed_enc, 'b', lw=0.5, label='Measured Velocity')
    l_plot.plot(time_arange, l_speed_actual, 'k', label='Actual Velocity')
    r_plot.plot(time_arange, r_speed_actual, 'k', label='Actual Velocity')
    
    l_plot.legend()
    r_plot.legend()
    

    plt.tight_layout()


    print(np.shape(l_speed_enc))
    # scale = 0.25
    # plt.xlim(-1*scale,scale)
    # plt.ylim(-1*scale,scale)
    
    plt.show()

def panel_bounds_test():
    area = SolarPanelArea(10,10,100)
    print(f"TRUE: {area.is_on_panel(np.array([0,0]))}")
    print(f"FALSE: {area.is_on_panel(np.array([-0.1,11]))}")
    
def limit_switch_test():
    # Simulation init
    area = SolarPanelArea(1,1,100)
    rover = Rover(area, 0.01, position=np.array([0.5,0.5]), orientation=np.array([0,1]))
    N = 1000
    
    # Default timeline arrays.
    # Indexing is [switch_number][time] or [switch_number][time][coordinate (x or y)]
    pos_timeline = np.zeros([8,1,2])
    status_timeline = np.full([8,1], True)
    
    # get the full limit switch readout from Rover
    pos_array = rover.get_limit_switch_readout(type='pos')
    status_array = rover.get_limit_switch_readout()

    # Initialize/setup plotting
    fig, ax = plt.subplots(1,1)
    fig.set_size_inches(16,9)
    ax.set_aspect('equal')
    ax.set(xlim=[-0.25,1.25],ylim=[-0.25,1.25])
    
    for i, pos in enumerate(pos_array):
        pos_timeline[i,0] = pos
        status_timeline[i,0] = status_array[i]

    plots = list(ax.plot(*switch_pos[-1], 'bo') for switch_pos in pos_timeline)
    
    ax.add_patch(patches.Rectangle((0,0), area.width, area.height, linewidth=1, edgecolor='r', facecolor='none'))
    
    rover.set_trajectory(0.05,0)
    for t in range(N):
        rover.update_sensors()
        rover.update_motors(use_sensors=True)
        rover.update_position()
        pos_array = np.array(rover.get_limit_switch_readout(type='pos')).reshape((8,1,2))
        status_array = np.array(rover.get_limit_switch_readout()).reshape(8,1)
        if not all(status_array.flatten()):
            rover.set_trajectory(0,0)



        
        pos_timeline = np.append(pos_timeline, pos_array, axis=1)
        status_timeline = np.append(status_timeline, status_array, axis=1)
    
    def animate(i):
        for switch, status, plot in zip(pos_timeline, status_timeline, plots):
            x,y = switch[i]
            state = status[i]
            plot[0].set_data([x],[y])
            if state:
                plot[0].set_color('b')
            else:
                plot[0].set_color('r')
                
        return plots
            
    ani = FuncAnimation(
        fig,
        animate,
        interval=10,
        blit=False,
        frames=range(1,N),
        repeat_delay=100
    )
    plt.show()


    # fig, ax = plt.subplots(1,1)
    # path, = ax.plot(plot_xs, plot_ys, 'k--', label='Rover path')
    # r_point, = ax.plot(0,0,"ro", label='Rover CG')
    
    # arr_scale = 0.0075
    # or_arrow = ax.arrow(0,0,0,0 , head_width=0.0025, head_length=0.001, color='r', ec=None, label='Rover orientation')
    # ax.set_aspect('equal')
    # ax.set_title("Rover circular path demonstration")
    # ax.legend(loc='center', ncol=1, fancybox=True, shadow=True)

    # def animate(i):
    #     x, y = plot_xs[:i], plot_ys[:i]
    #     or_x, or_y = or_xs[i], or_ys[i]
    #     path.set_data(x, y)
    #     r_point.set_data([x[-1]],[y[-1]])
    #     or_arrow.set_data(x=x[-1],y=y[-1], dx=arr_scale*or_x, dy=arr_scale*or_y)
    #     return path, r_point
    
    # ani = FuncAnimation(
    #     fig,
    #     animate,
    #     interval=10,
    #     blit=False,
    #     frames=range(1,len(plot_xs)),
    #     repeat_delay=100
    # )
    
    # writer = animation.PillowWriter(fps=60,
    #                                 bitrate=1800)
    # ani.save('movement.gif', writer=writer)
    
    
    # lfo_pos = rover.limit_switch_lfo.get_position(rover.positional_information.position, rover.get_azimuth())
    # lfi_pos = rover.limit_switch_lfi.get_position(rover.positional_information.position, rover.get_azimuth())
    # rfo_pos = rover.limit_switch_rfo.get_position(rover.positional_information.position, rover.get_azimuth())
    # rfi_pos = rover.limit_switch_rfi.get_position(rover.positional_information.position, rover.get_azimuth())
    # lbo_pos = rover.limit_switch_lbo.get_position(rover.positional_information.position, rover.get_azimuth())
    # lbi_pos = rover.limit_switch_lbi.get_position(rover.positional_information.position, rover.get_azimuth())
    # rbo_pos = rover.limit_switch_rbo.get_position(rover.positional_information.position, rover.get_azimuth())
    # rbi_pos = rover.limit_switch_rbi.get_position(rover.positional_information.position, rover.get_azimuth())
    
    # plt.plot(*lfo_pos, 'bo')
    # plt.plot(*lfi_pos, 'bo')
    # plt.plot(*rfo_pos, 'bo')
    # plt.plot(*rfi_pos, 'bo')
    # plt.plot(*lbo_pos, 'bo')
    # plt.plot(*lbi_pos, 'bo')
    # plt.plot(*rbo_pos, 'bo')
    # plt.plot(*rbi_pos, 'bo')
    # plt.plot(*rover.positional_information.position, 'b+')
    
    
    # rover.set_trajectory(0,0.7)
    # for t in range(145):
    #     rover.update_sensors()

    #     rover.update_motors(use_sensors=False)
    #     rover.update_position()
    
    # lfo_pos = rover.limit_switch_lfo.get_position(rover.positional_information.position, rover.get_azimuth())
    # lfi_pos = rover.limit_switch_lfi.get_position(rover.positional_information.position, rover.get_azimuth())
    # rfo_pos = rover.limit_switch_rfo.get_position(rover.positional_information.position, rover.get_azimuth())
    # rfi_pos = rover.limit_switch_rfi.get_position(rover.positional_information.position, rover.get_azimuth())
    # lbo_pos = rover.limit_switch_lbo.get_position(rover.positional_information.position, rover.get_azimuth())
    # lbi_pos = rover.limit_switch_lbi.get_position(rover.positional_information.position, rover.get_azimuth())
    # rbo_pos = rover.limit_switch_rbo.get_position(rover.positional_information.position, rover.get_azimuth())
    # rbi_pos = rover.limit_switch_rbi.get_position(rover.positional_information.position, rover.get_azimuth())
    
    # plt.plot(*lfo_pos, 'ro')
    # plt.plot(*lfi_pos, 'ro')
    # plt.plot(*rfo_pos, 'ro')
    # plt.plot(*rfi_pos, 'ro')
    # plt.plot(*lbo_pos, 'ro')
    # plt.plot(*lbi_pos, 'ro')
    # plt.plot(*rbo_pos, 'ro')
    # plt.plot(*rbi_pos, 'ro')
    # plt.plot(*rover.positional_information.position, 'r+')
        
def rotational_pid_test():

    N = 1000
        
    xs = np.linspace(0,N*0.01,N)
    
    fig, (ax1, ax2) = plt.subplots(1,2)
    fig.set_size_inches(16,9)
    # ax1.set_ylim(0,1.5)
    ax1.set_xlim(0,xs[-1])
    runs = 20
    
    
    offset = []
    
    for r in range(runs):
        panel = SolarPanelArea(1,1,100)
        rover = Rover(panel, 0.01, np.array([0.5,0.5]), np.array([1,0]))        
        az_list = []
        desired_az = []
        estimated_az = []
        rate_list = []
        desired_rate_list = []
        # turn_magnitude = np.random.choice([-1,1])*((np.random.rand())*np.pi/4 + np.pi/2) # turns near +-pi/2
        turn_magnitude = (np.pi/2) # Turns at exactly +-pi/2
        

        rover.set_desired_azimuth(turn_magnitude)
        for t in range(N):
            rover.update_sensors()            
            _, desired = rover.update_turning_trajectory(use_sensors=True)
            rover.update_motors(use_sensors=True)
            rover.update_position()
            _, actual = rover.compute_trajectory(use_sensors=False)

            
            estimated_az.append(rover.estimated_pos.azimuth)
            rate_list.append(actual)
            desired_rate_list.append(desired)
            az_list.append(rover.get_azimuth())
            
            desired_az.append(rover.desired_azimuth)

        ax1.plot(xs, np.rad2deg(az_list), 'b', linewidth=min(20/runs,1))
        ax1.plot(xs, np.rad2deg(estimated_az), 'r', linewidth=min(20/runs,1))
        
        offset.append(((az_list[-1] - desired_az[-1] + np.pi)%(2*np.pi) - np.pi)/turn_magnitude)
        
    # print(np.average(offset))
    ax1.plot(xs, np.rad2deg(desired_az), 'k--')
    ax1.set_ylim(85,95)
    
    
    # n = runs//10
    # p,x = np.histogram(offset, bins=n)
    # x = x[:-1] + (x[1] - x[0])/2    
    # f1 = UnivariateSpline(x, p, s=n)
    # f2 = UnivariateSpline(x, p, s=runs)
    # ax2.plot(x, f1(x), 'b', linewidth=0.5)
    # ax2.plot(x, f2(x), 'k--')
    

    

    plt.show()

def linear_pid_test():

    N = 500
        
    xs = np.linspace(0,N*0.01,N)
    dt = 0.01
    
    fig, (ax1, ax2, ax3, ax4) = plt.subplots(1,4)
    fig.set_size_inches(16,9)
    ax1.set_xlim(0,xs[-1])
    runs = 1
    
    
    offset = []
    
    for r in range(runs):
        panel = SolarPanelArea(1,1,100)
        rover = Rover(panel, 0.01, np.array([0,0]), np.array([1,0]))   
        # rover.set_trajectory(0.05,0)

        pos_list = []
        est_pos_list = []
        est_vel_list = []
        vel_list = []
        accel_list = []
        imu_accel_list = []
        imu_vel_list = [0]
        imu_pos_list = [0]
        state_list = []
        y_list = []
        y_est_list = []

        rover.set_desired_distance(0.1)
        for t in range(N):
            # if rover.motor_state:
            #     a, b = rover.update_positional_trajectory()
            rover.update_positional_trajectory()
            rover.update_sensors()

            rover.make_decision()
            state_list.append(rover.motor_state)
            pos_list.append(rover.positional_information.position[0])
            y_list.append(rover.positional_information.position[1])
            vel_list.append(rover.positional_information.linear_velocity)
            accel_list.append(rover.positional_information.linear_accel)
            est_pos_list.append(rover.estimated_pos.position[0])
            y_est_list.append(rover.estimated_pos.position[1])
            est_vel_list.append(rover.estimated_pos.linear_velocity)
            imu_accel_list.append(rover.imu_info[0][0])
            imu_vel_list.append(imu_vel_list[-1] + imu_accel_list[-1]*dt)
            imu_pos_list.append(imu_pos_list[-1] + imu_vel_list[-1]*dt)

            rover.update_motors(use_sensors=True)
            rover.update_position()

        imu_vel_list = imu_vel_list[1:]
        imu_pos_list = imu_pos_list[1:]

        ax1.plot(xs, accel_list, 'k--')
        ax1.plot(xs, imu_accel_list, 'r')
        
        ax2.plot(xs, vel_list, 'k--')
        ax2.plot(xs, est_vel_list, 'b')
        ax2.plot(xs, imu_vel_list, 'r')
        # ax2.plot(xs, state_list, 'g')
        ax3.plot(xs, np.full_like(xs, 0.1), 'g')
        ax3.plot(xs, est_pos_list, 'b')
        ax3.plot(xs, pos_list, 'k--')
        # ax3.plot(xs, state_list, 'g')

        ax3.plot(xs, imu_pos_list, 'r')
        ax4.plot(pos_list, y_list, 'k--')
        ax4.set_xlim(0,0.2)
        ax4.set_ylim(-0.1,0.1)
        ax4.plot(est_pos_list, y_est_list, 'r')
    plt.show()
    pass
    
def rot_ang():

    motor = DCMotorDiscrete(K=1.14, J=1.66E-4, L=10e-3, dt=0.001)

    motor.update(12)
    x = motor.get_angular_acceleration()
    print(x)

def state_tester():
    dt = 0.01 
    panel = SolarPanelArea(1,1,100)
    
    starting_position = np.array([0.5, 0.5])
    starting_orientation = np.array([np.cos(0), np.sin(0)])
    rover = Rover(panel, dt, starting_position, starting_orientation)
    rover.estimated_pos.position = starting_position
    rover.estimated_pos.orientation = starting_orientation
    time = 100000
    show_every = 50
    
    N = int(time // dt)
    
    #Fill buffer
    for t in range(100):
        rover.simulate()
        # print(f"position: \t{rover.positional_information.position}\nradio_message: \t{rover.radio_message}\n")
    

    rover.set_radio_message(RadioMessage.STARTCLEANINGOK)
    # for t in range(N):
    #     rover.simulate()
    #     # print(f"position: \t\t{rover.positional_information.position}\ndecision_state: \t{rover.decision_state}\n")
    #     rover.get_limit_switch_readout(display=True, type='pos')
    #     pass


    # get the full limit switch readout from Rover
    pos_array = rover.get_limit_switch_readout(type='pos')
    status_array = rover.get_limit_switch_readout()
    
    center_xs = []
    center_ys = []
    est_center_xs = []
    est_center_ys = []
    pos_timeline = np.zeros([8,1,2])
    status_timeline = np.full([8,1], True)
    
    
    

    # Initialize/setup plotting
    fig, ax = plt.subplots(1,1)
    fig.set_size_inches(16,9)
    ax.set_aspect('equal')
    ax.set(xlim=[-0.25,1.25],ylim=[-0.25,1.25])
    
    for i, pos in enumerate(pos_array):
        pos_timeline[i,0] = pos
        status_timeline[i,0] = status_array[i]

    plots = list(ax.plot(*switch_pos[-1], 'bo', label='Limit Switch') for switch_pos in pos_timeline)
    
    center_pos, = ax.plot(starting_position[0], starting_position[1], 'go', label='Real Position')
    estimated_pos, = ax.plot(starting_position[0], starting_position[1], 'ko', label='Estimated Position')
    
    center_path, = ax.plot([starting_position[0]], [starting_position[1]], 'g-')
    estimated_path, = ax.plot([starting_position[0]], [starting_position[1]], 'k--')

    ax.add_patch(patches.Rectangle((0,0), panel.width, panel.height, linewidth=1, edgecolor='r', facecolor='none'))
    
    # Search For Corner Step
    for t in range(N):
        rover.simulate()
        pos_array = np.array(rover.get_limit_switch_readout(type='pos')).reshape((8,1,2))
        status_array = np.array(rover.get_limit_switch_readout()).reshape(8,1)
        
        
        center_xs.append(rover.positional_information.position[0])
        center_ys.append(rover.positional_information.position[1])
        
        est_center_xs.append(rover.estimated_pos.position[0])
        est_center_ys.append(rover.estimated_pos.position[1])
        

        pos_timeline = np.append(pos_timeline, pos_array, axis=1)
        status_timeline = np.append(status_timeline, status_array, axis=1)
        print(f"corner_state: \t{rover.search_for_corner_state}")
        if rover.search_for_corner_state == SearchForCornerStates.DONE:
            break
    
    # Outer Loop Step
    for t in range(N):
        rover.simulate()
        pos_array = np.array(rover.get_limit_switch_readout(type='pos')).reshape((8,1,2))
        status_array = np.array(rover.get_limit_switch_readout()).reshape(8,1)
        
        center_xs.append(rover.positional_information.position[0])
        center_ys.append(rover.positional_information.position[1])
        
        est_center_xs.append(rover.estimated_pos.position[0])
        est_center_ys.append(rover.estimated_pos.position[1])        

        pos_timeline = np.append(pos_timeline, pos_array, axis=1)
        status_timeline = np.append(status_timeline, status_array, axis=1)
        print(f"outer_state: \t{rover.outer_loop_states}")
        if rover.outer_loop_states == OuterLoopStates.DONE:
            break
        
    # Inner Loop Step
    for t in range(N):
        rover.simulate()
        pos_array = np.array(rover.get_limit_switch_readout(type='pos')).reshape((8,1,2))
        status_array = np.array(rover.get_limit_switch_readout()).reshape(8,1)
        
        center_xs.append(rover.positional_information.position[0])
        center_ys.append(rover.positional_information.position[1])
        
        est_center_xs.append(rover.estimated_pos.position[0])
        est_center_ys.append(rover.estimated_pos.position[1])        

        pos_timeline = np.append(pos_timeline, pos_array, axis=1)
        status_timeline = np.append(status_timeline, status_array, axis=1)
        print(f"inner_state: \t{rover.inner_loop_states}\nnodes: {rover.panel_width_nodes, rover.panel_height_nodes}")
        if rover.radio_message == RadioMessage.ERROR:
            print("ERRORED OUT")
            break
        if rover.inner_loop_states == InnerLoopStates.DONE:
            break          
            
        
    
    def animate(i):
        center_pos.set_data([center_xs[show_every*i]],[center_ys[show_every*i]])
        estimated_pos.set_data([est_center_xs[show_every*i]],[est_center_ys[show_every*i]])

        center_path.set_data(center_xs[:show_every*i],center_ys[:show_every*i])
        estimated_path.set_data(est_center_xs[:show_every*i],est_center_ys[:show_every*i])
        for switch, status, plot in zip(pos_timeline, status_timeline, plots):
            x,y = switch[show_every*i]
            state = status[show_every*i]
            plot[0].set_data([x],[y])
            if state:
                plot[0].set_color('b')
            else:
                plot[0].set_color('r')
                
        return plots, center_pos, estimated_pos, center_path, estimated_path
    
    ax.legend()
    ani = FuncAnimation(
        fig,
        animate,
        interval=100,
        blit=False,
        frames=range(1,int(len(center_xs))),
        repeat_delay=100
    )
    
    # ani.save("rover_mission.gif")
    plt.show()


if __name__ == '__main__':
    # Write which test you want to run here

    # motor_test()
    # visualization_test()
    # panel_test()

    # derivative_error_test()
    # imu_test()

    # rover_movement_test()
    # # rotary_encoder_test()
    # rover_sensor_movement_test()
    # panel_bounds_test()
    # limit_switch_test()
    # rotational_pid_test()
    # linear_pid_test()
    # rot_ang()
    
    state_tester()
    

    pass
