pcarlss/Solar-Panel-Cleaning-Drone/Simulations/Edge-Detection-Camera/esp32.cpp

#include "esp_camera.h"
#include <Arduino.h>

// Pin configuration for ESP32-CAM
#define PWDN_GPIO_NUM -1
#define RESET_GPIO_NUM -1
#define XCLK_GPIO_NUM 0
#define SIOD_GPIO_NUM 26
#define SIOC_GPIO_NUM 27
#define Y9_GPIO_NUM 35
#define Y8_GPIO_NUM 34
#define Y7_GPIO_NUM 39
#define Y6_GPIO_NUM 36
#define Y5_GPIO_NUM 21
#define Y4_GPIO_NUM 19
#define Y3_GPIO_NUM 18
#define Y2_GPIO_NUM 5
#define VSYNC_GPIO_NUM 25
#define HREF_GPIO_NUM 23
#define PCLK_GPIO_NUM 22

// Grid size for edge detection
const int GRID_SIZE = 3;

// Threshold for edge detection
const int EDGE_THRESHOLD = 40;

// Initialize the camera
void setup_camera()
{
  camera_config_t config;
  config.ledc_channel = LEDC_CHANNEL_0;
  config.ledc_timer = LEDC_TIMER_0;
  config.pin_d0 = Y2_GPIO_NUM;
  config.pin_d1 = Y3_GPIO_NUM;
  config.pin_d2 = Y4_GPIO_NUM;
  config.pin_d3 = Y5_GPIO_NUM;
  config.pin_d4 = Y6_GPIO_NUM;
  config.pin_d5 = Y7_GPIO_NUM;
  config.pin_d6 = Y8_GPIO_NUM;
  config.pin_d7 = Y9_GPIO_NUM;
  config.pin_xclk = XCLK_GPIO_NUM;
  config.pin_pclk = PCLK_GPIO_NUM;
  config.pin_vsync = VSYNC_GPIO_NUM;
  config.pin_href = HREF_GPIO_NUM;
  config.pin_sscb_sda = SIOD_GPIO_NUM;
  config.pin_sscb_scl = SIOC_GPIO_NUM;
  config.pin_pwdn = PWDN_GPIO_NUM;
  config.pin_reset = RESET_GPIO_NUM;
  config.xclk_freq_hz = 20000000;
  config.pixel_format = PIXFORMAT_GRAYSCALE;

  // Initialize the camera
  if (esp_camera_init(&config) != ESP_OK)
  {
    Serial.println("Camera init failed");
    while (true)
      ;
  }
}

void setup()
{
  Serial.begin(115200);
  setup_camera();
}

void loop()
{
  // Capture a frame
  camera_fb_t *frame = esp_camera_fb_get();
  if (!frame)
  {
    Serial.println("Camera capture failed");
    return;
  }

  // Process the frame to detect edges and regions (code to be filled based on OpenCV approach)

  // Output grid signals
  Serial.println("Edge Signals (3x3 Grid):");
  Serial.println("[0 1 0]");
  Serial.println("[1 0 1]");
  Serial.println("[0 1 0]");

  // Return the frame buffer to the driver
  esp_camera_fb_return(frame);

  delay(500); // Slow down the loop for debugging
}
